seanwatson/ece4416-project/software/embedded/serial_forwarder/serial_forwarder.ino

/*********************************************************
* 
* File:     serial_forwarder.ino
* Author:   Sean Watson
* Date:     Jan 2013
*
* Description: Forwards any serial communication over
*              USB through to the Bluetooth module and
*              vice versa
*
* Copyright (c) 2013 Sean Watson
* Licensed under the MIT license
*
**********************************************************/

long usb_baud = 115200;  // USB baud rate
long bt_baud = 115200;   // Bluetooth baud rate

void setup(){
  
  // Setup the serial channels
  Serial.begin(usb_baud);
  Serial1.begin(bt_baud);
}

void loop(){
  
  // Forward USB to Bluetooth
  if(Serial.available()){
    Serial1.write(Serial.read());
  }
  
  // Forward Bluetooth to USB
  if(Serial1.available()){
    Serial.write(Serial1.read());
  }
}
